lacduong/TacLINK/Experimental data/force_resconstruction/new/P0.0kPa_Trial5_1.PNG

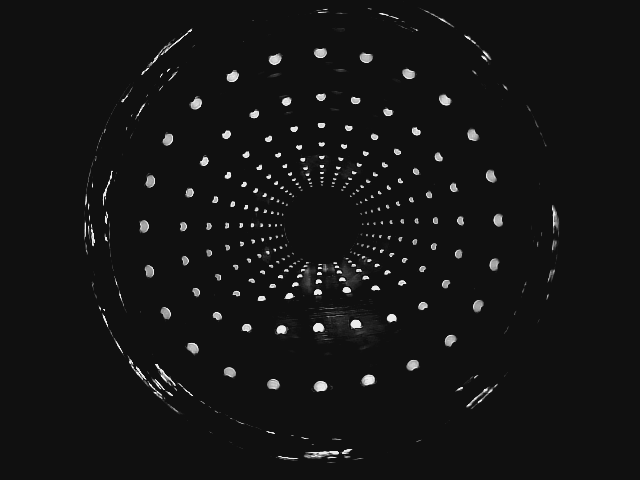
Experimental data/force_resconstruction/new/P0.0kPa_Trial5_1.PNG
