lacduong/TacLINK/Experimental data/force_resconstruction/new/P0.5kPa_Trial2_1.PNG

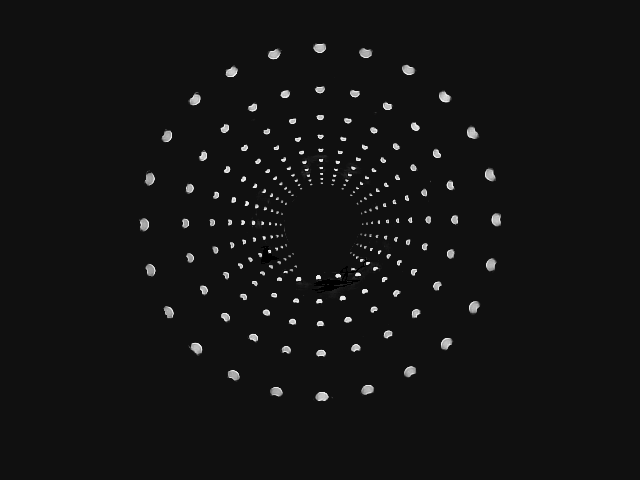
Experimental data/force_resconstruction/new/P0.5kPa_Trial2_1.PNG
