lacduong/TacLINK/Experimental data/final_experiment/ForceData/InitTrial001.CSV

Test No.
Title
Tester
Channel No. | 1 | 2 | 3 | 4
Channel Name | Fx-1 | Fy-1 | Fz-1 | Mark
Unit | N | N | N
Number of data | 150 | 150 | 150 | 150
maximum value | 0.02925 | 0.02603 | 0.03120 | 0
minimum value | -0.01497 | -0.01311 | -0.06188 | 0
0.000000 | 0.00000 | 0.00000 | 0.00000 | 0
0.100000 | 0.00000 | 0.00000 | 0.00000 | 0
0.200000 | 0.00000 | 0.00000 | 0.00000 | 0
0.300000 | 0.00000 | 0.00000 | 0.00000 | 0
0.400000 | 0.00000 | 0.00000 | 0.00000 | 0
0.500000 | 0.00000 | 0.00000 | 0.00000 | 0
0.600000 | -0.01447 | -0.00019 | -0.00008 | 0
0.700000 | -0.00031 | 0.00007 | -0.03104 | 0
0.800000 | -0.00025 | 0.01292 | 0.00013 | 0
0.900000 | 0.00000 | 0.00000 | 0.00000 | 0
1.000000 | 0.00000 | 0.00000 | 0.00000 | 0
1.100000 | 0.00000 | 0.00000 | 0.00000 | 0
1.200000 | 0.00000 | 0.00000 | 0.00000 | 0
1.300000 | 0.00000 | 0.00000 | 0.00000 | 0
1.400000 | 0.00000 | 0.00000 | 0.00000 | 0
1.500000 | -0.01447 | -0.00019 | -0.00008 | 0
1.600000 | 0.00000 | 0.00000 | 0.00000 | 0
1.700000 | -0.00025 | 0.01292 | 0.00013 | 0
1.800000 | -0.01447 | -0.00019 | -0.00008 | 0
1.900000 | -0.01422 | -0.01311 | -0.00021 | 0
2.000000 | -0.01447 | -0.00019 | -0.00008 | 0
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
