lacduong/TacLINK/Experimental data/final_experiment/ForceData/J10R5Trial002.CSV

Test No.
Title
Tester
Channel No. | 1 | 2 | 3 | 4
Channel Name | Fx-1 | Fy-1 | Fz-1 | Mark
Unit | N | N | N
Number of data | 444 | 444 | 444 | 444
maximum value | 0.01579 | 0.05157 | 0.15569 | 0
minimum value | -0.04266 | -0.00055 | 0.06235 | 0
0.000000 | 0.00132 | 0.01255 | 0.15535 | 0
0.100000 | 0.00132 | 0.01255 | 0.15535 | 0
0.200000 | 0.00106 | 0.02547 | 0.15548 | 0
0.300000 | 0.00132 | 0.01255 | 0.15535 | 0
0.400000 | 0.01553 | 0.02566 | 0.15556 | 0
0.500000 | 0.00075 | 0.02555 | 0.12444 | 0
0.600000 | 0.01579 | 0.01274 | 0.15543 | 0
0.700000 | 0.00075 | 0.02555 | 0.12444 | 0
0.800000 | 0.00100 | 0.01263 | 0.12431 | 0
0.900000 | 0.00075 | 0.02555 | 0.12444 | 0
1.000000 | -0.01372 | 0.02536 | 0.12437 | 0
1.100000 | 0.00075 | 0.02555 | 0.12444 | 0
1.200000 | -0.01372 | 0.02536 | 0.12437 | 0
1.300000 | 0.00075 | 0.02555 | 0.12444 | 0
1.400000 | 0.00075 | 0.02555 | 0.12444 | 0
1.500000 | 0.00075 | 0.02555 | 0.12444 | 0
1.600000 | 0.00106 | 0.02547 | 0.15548 | 0
1.700000 | 0.00075 | 0.02555 | 0.12444 | 0
1.800000 | 0.01522 | 0.02573 | 0.12452 | 0
1.900000 | -0.01397 | 0.03828 | 0.12450 | 0
2.000000 | 0.00075 | 0.02555 | 0.12444 | 0
2.100000 | 0.00100 | 0.01263 | 0.12431 | 0
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
