lacduong/TacLINK/Experimental data/final_experiment/Init/InitTrial5_1.PNG

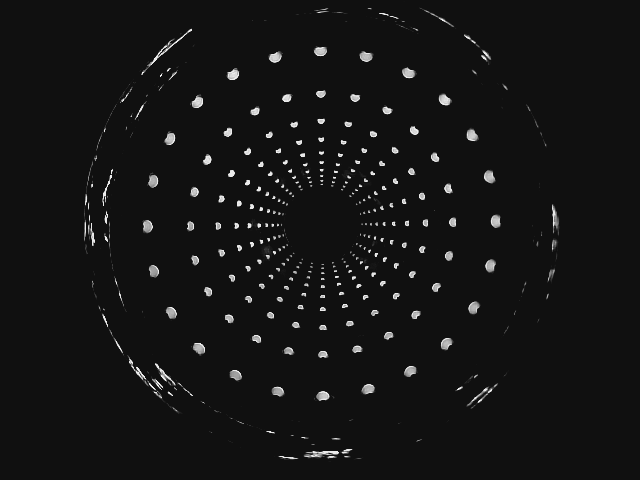
Experimental data/final_experiment/Init/InitTrial5_1.PNG
