lacduong/TacLINK/Experimental data/final_experiment/Init/InitTrial6_2.PNG

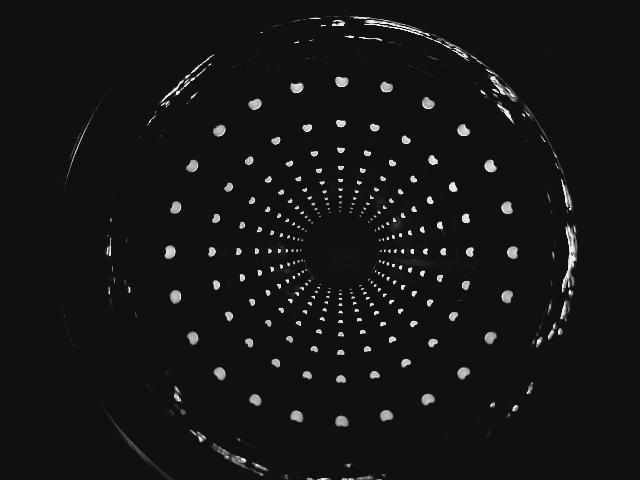
Experimental data/final_experiment/Init/InitTrial6_2.PNG
