lacduong/TacLINK/Experimental data/final_experiment/J5/J5R10Trial6_2.PNG

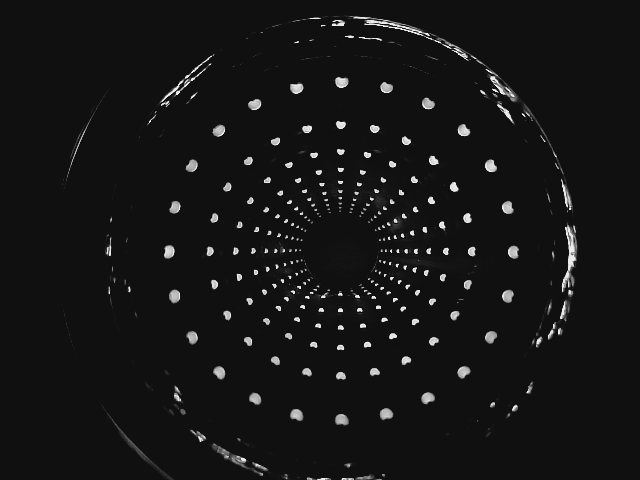
Experimental data/final_experiment/J5/J5R10Trial6_2.PNG
