lacduong/TacLINK/Experimental data/final_experiment/J9/J9R5Trial7cam2.PNG

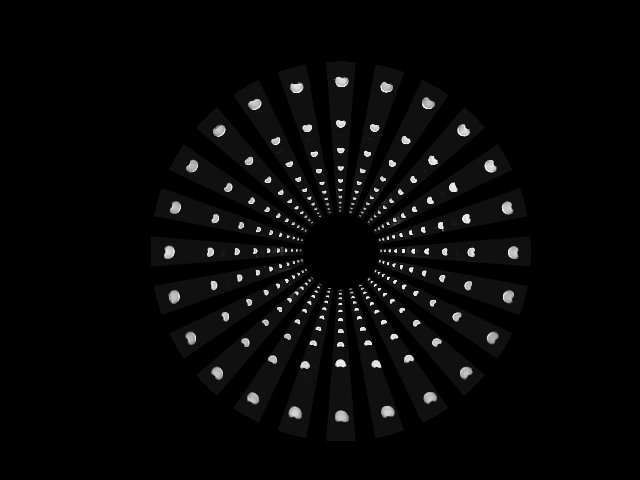
Experimental data/final_experiment/J9/J9R5Trial7cam2.PNG
