lacduong/TacLINK/Experimental data/source_force_data/J1/J1R0P0.0kPaTrial2cam1.PNG

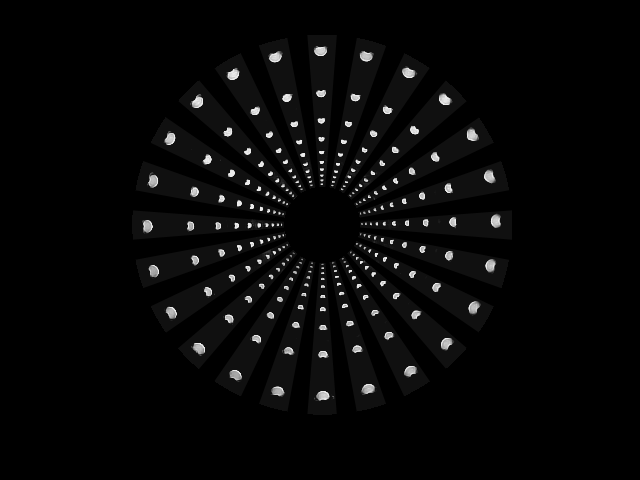
Experimental data/source_force_data/J1/J1R0P0.0kPaTrial2cam1.PNG
