lacduong/TacLINK/Experimental data/source_force_data/J1/J1R5P1.0kPaTrial8cam2.PNG

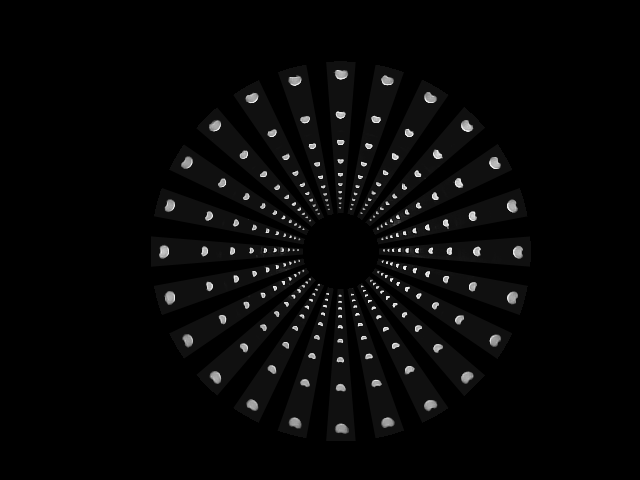
Experimental data/source_force_data/J1/J1R5P1.0kPaTrial8cam2.PNG
