lacduong/TacLINK/Experimental data/source_force_data/J1/R5/J1R5P0.5kPaTrial1cam1.PNG

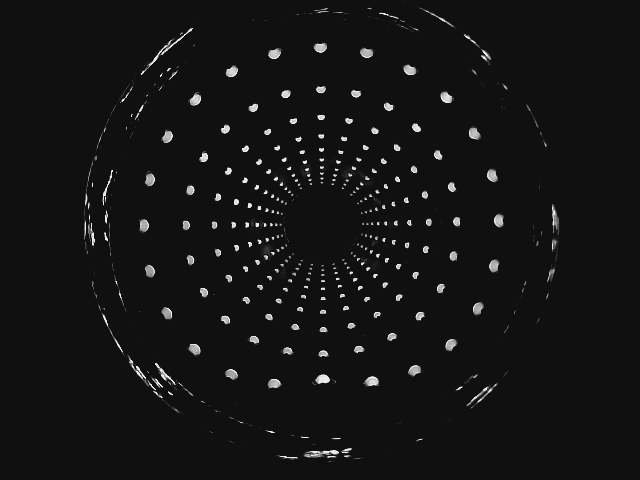
Experimental data/source_force_data/J1/R5/J1R5P0.5kPaTrial1cam1.PNG
