lacduong/TacLINK/Experimental data/source_force_data/J1/R5/J1R5P1.5kPaTrial4cam2.PNG

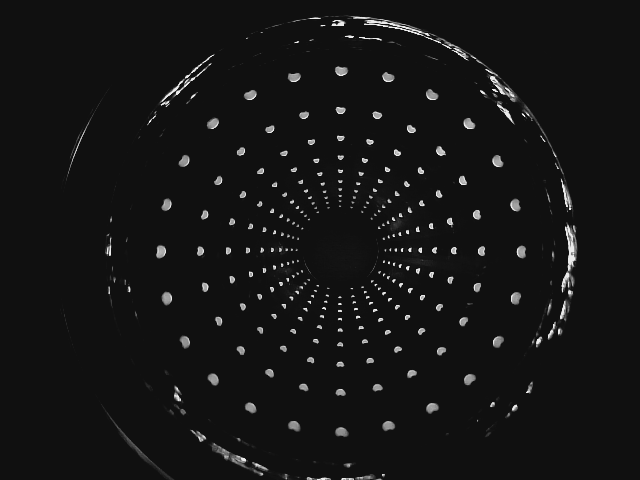
Experimental data/source_force_data/J1/R5/J1R5P1.5kPaTrial4cam2.PNG
