lacduong/TacLINK/Experimental data/source_force_data/J2/R5/J2R5P0.5kPaTrial3cam2.PNG

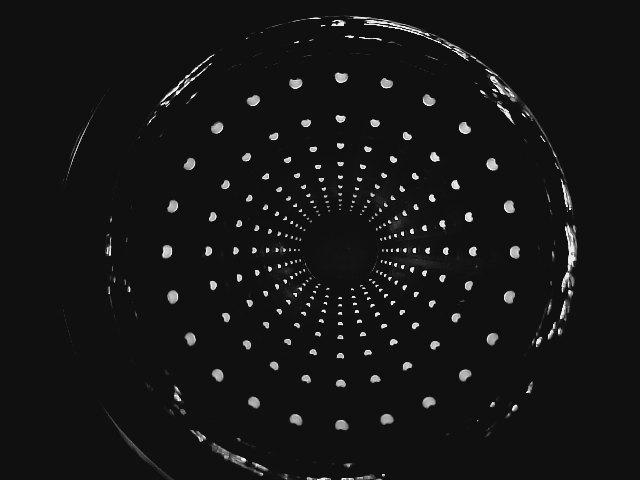
Experimental data/source_force_data/J2/R5/J2R5P0.5kPaTrial3cam2.PNG
