lacduong/TacLINK/Experimental data/source_force_data/J2/R10/J2R10P1.0kPaTrial4cam2.PNG

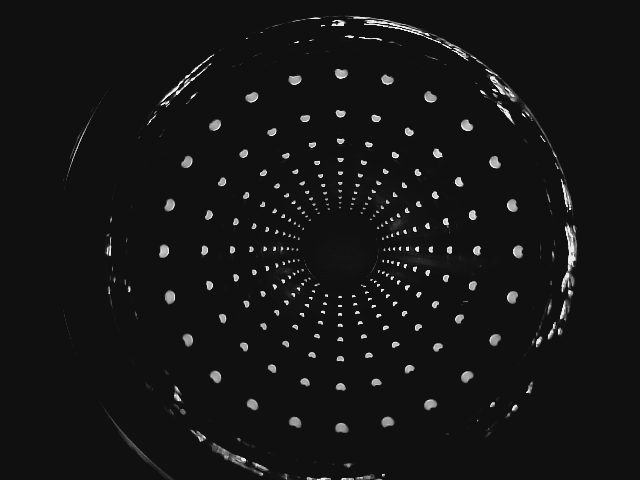
Experimental data/source_force_data/J2/R10/J2R10P1.0kPaTrial4cam2.PNG
