lacduong/TacLINK/Experimental data/source_force_data/J4/R10/J4R10P1.5kPaTrial7cam1.PNG

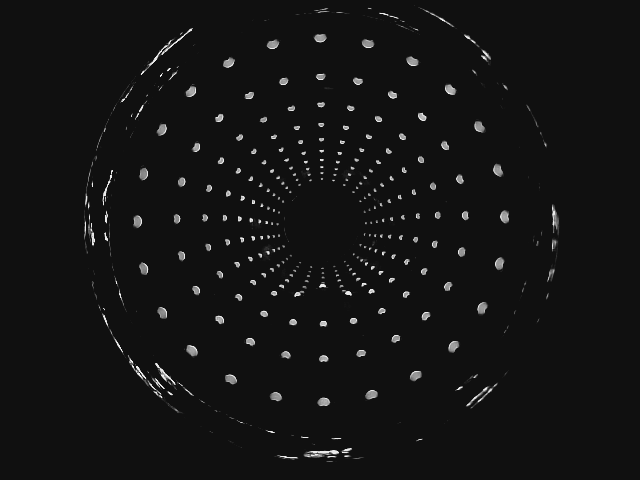
Experimental data/source_force_data/J4/R10/J4R10P1.5kPaTrial7cam1.PNG
