lacduong/TacLINK/Experimental data/source_force_data/J6/R5/J6R5P1.5kPaTrial8cam1.PNG

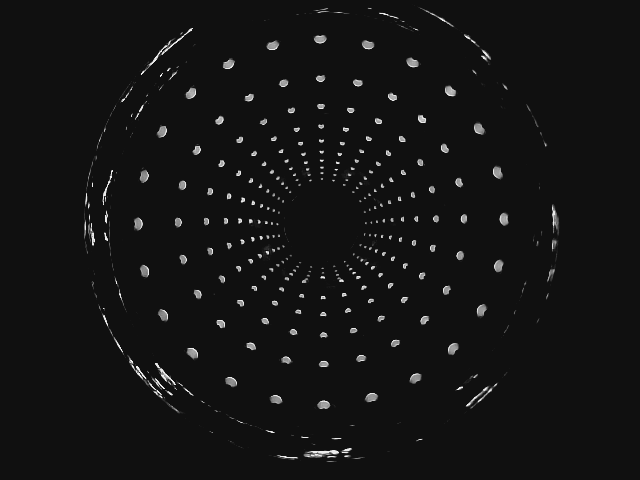
Experimental data/source_force_data/J6/R5/J6R5P1.5kPaTrial8cam1.PNG
