lacduong/TacLINK/Experimental data/source_force_data/J8/R5/J8R5P1.0kPaTrial9cam2.PNG

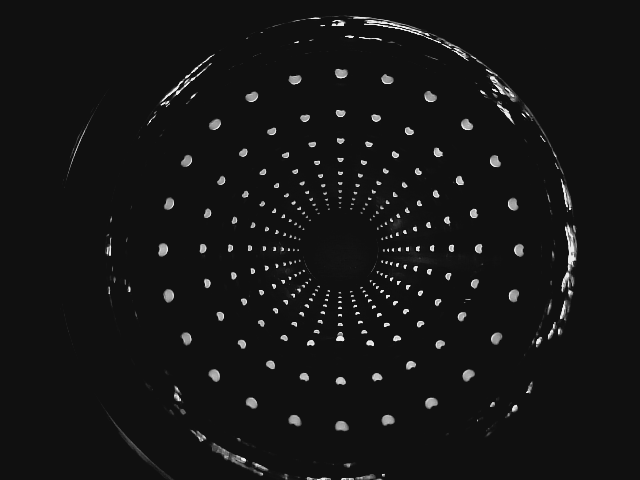
Experimental data/source_force_data/J8/R5/J8R5P1.0kPaTrial9cam2.PNG
