lacduong/TacLINK/Experimental data/source_force_data/J8/R10/J8R10P0.5kPaTrial1cam2.PNG

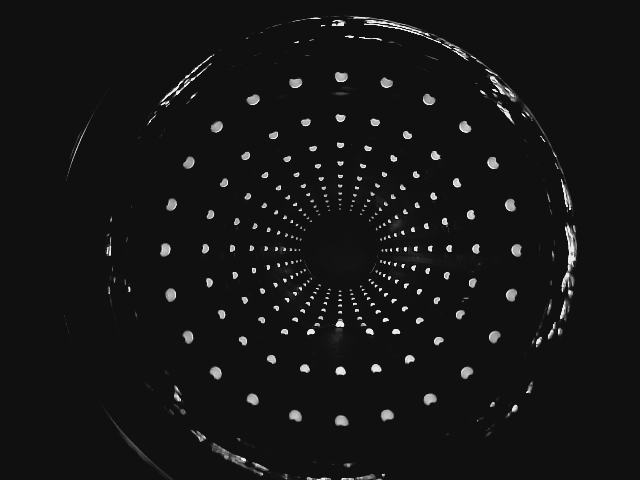
Experimental data/source_force_data/J8/R10/J8R10P0.5kPaTrial1cam2.PNG
