lacduong/TacLINK/Experimental data/source_force_data/J10/J10R5P0.0kPaTrial7cam2.PNG

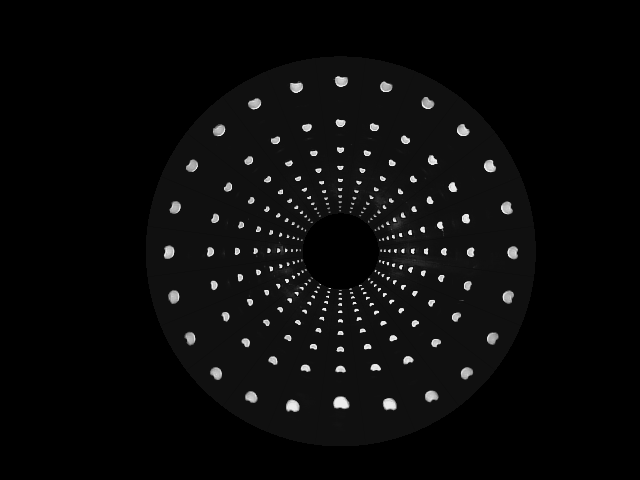
Experimental data/source_force_data/J10/J10R5P0.0kPaTrial7cam2.PNG
