lacduong/TacLINK/Experimental data/source_force_data/J10/J10R5P1.0kPaTrial2cam1.PNG

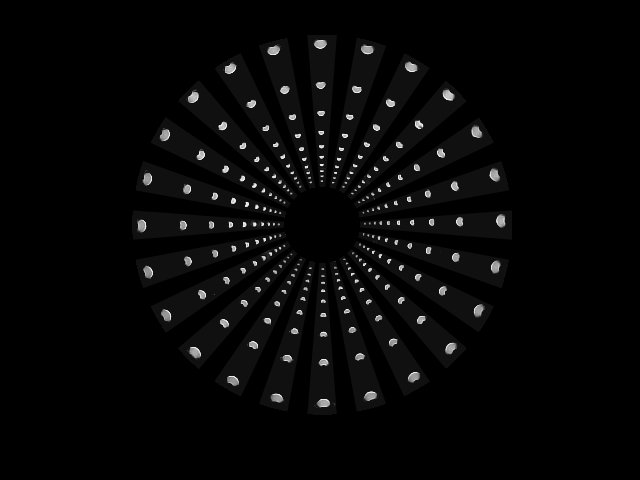
Experimental data/source_force_data/J10/J10R5P1.0kPaTrial2cam1.PNG
