lacduong/TacLINK/IEEE T-RO Final Latex Version/camera_tracking.pdf

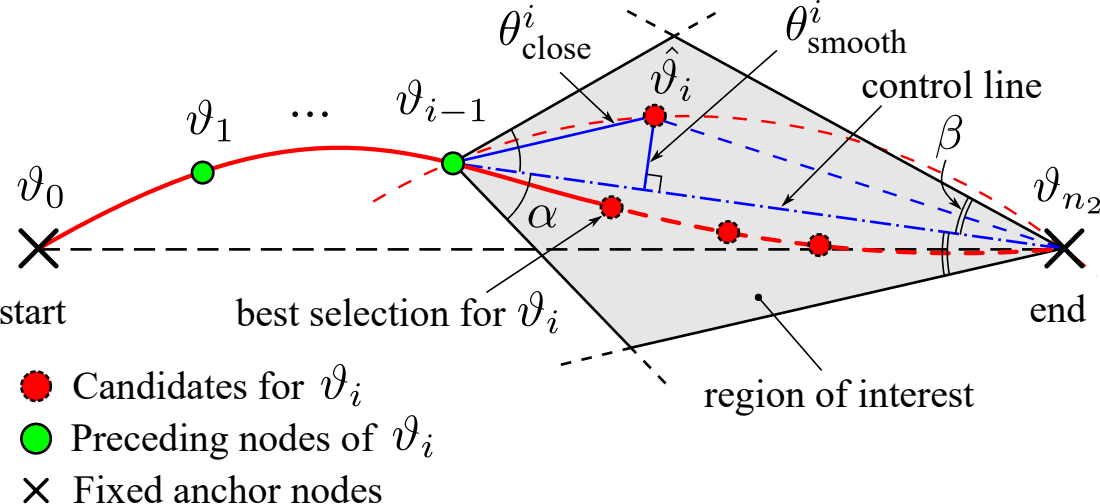
[picture p59: page 1]
smooth; start; end; close; control line

Candidates for
Preceding nodes of
Fixed anchor nodes

best selection for

region of interest
