lacduong/TacLINK/IEEE T-RO Final Latex Version/camera_variation.pdf

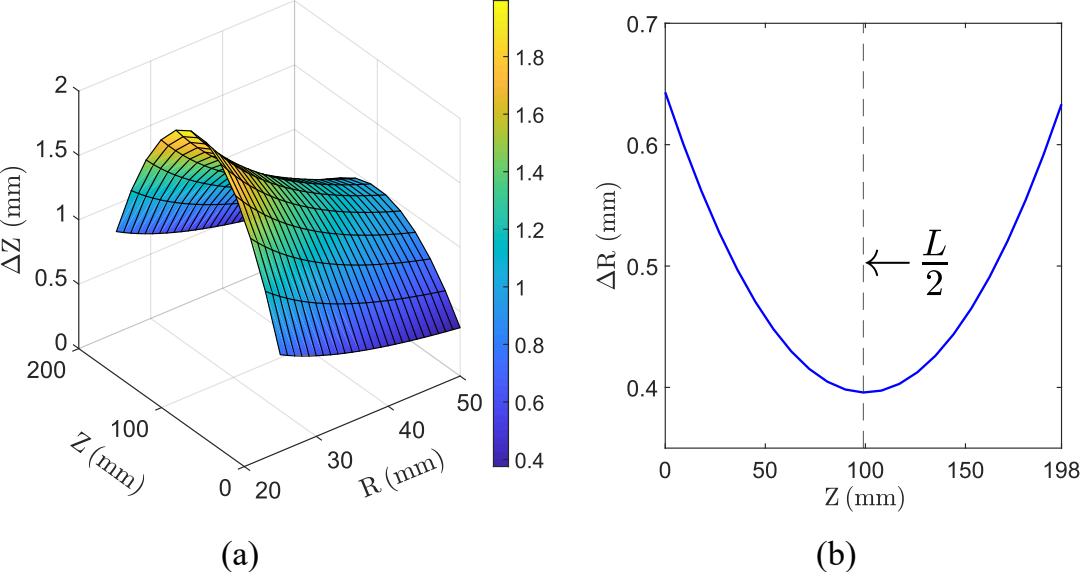
[picture p60: page 1]
