lacduong/TacLINK/IEEE T-RO Final Latex Version/fem_model.pdf

e

# cell

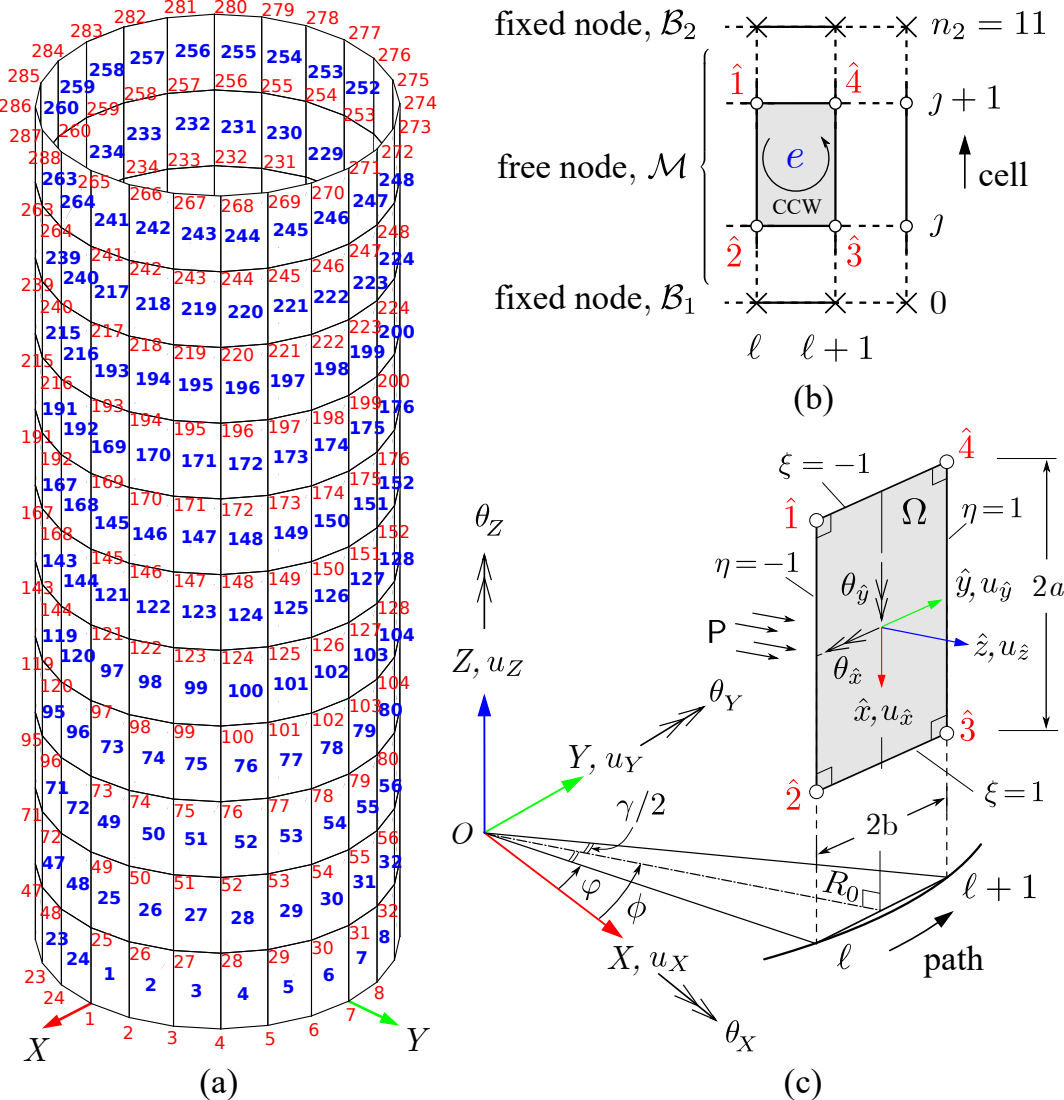
[picture p61: page 1]
CCW; path; fixed node; free node
