lacduong/TacLINK/IEEE T-RO Final Latex Version/fem_simulation.pdf

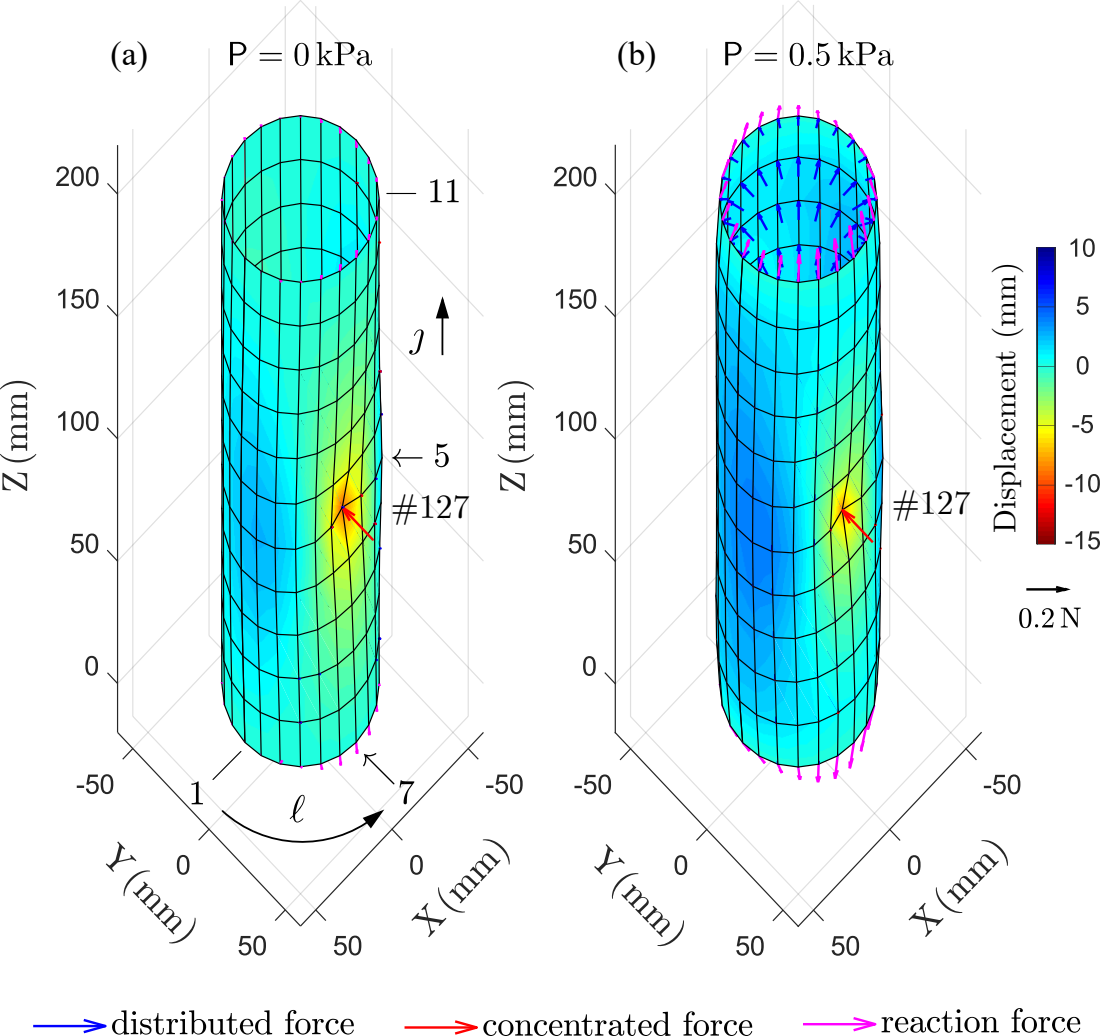
[picture p62: page 1]
Displacement (mm)
