lacduong/TacLINK/IEEE T-RO Final Latex Version/force_singlepoint.pdf

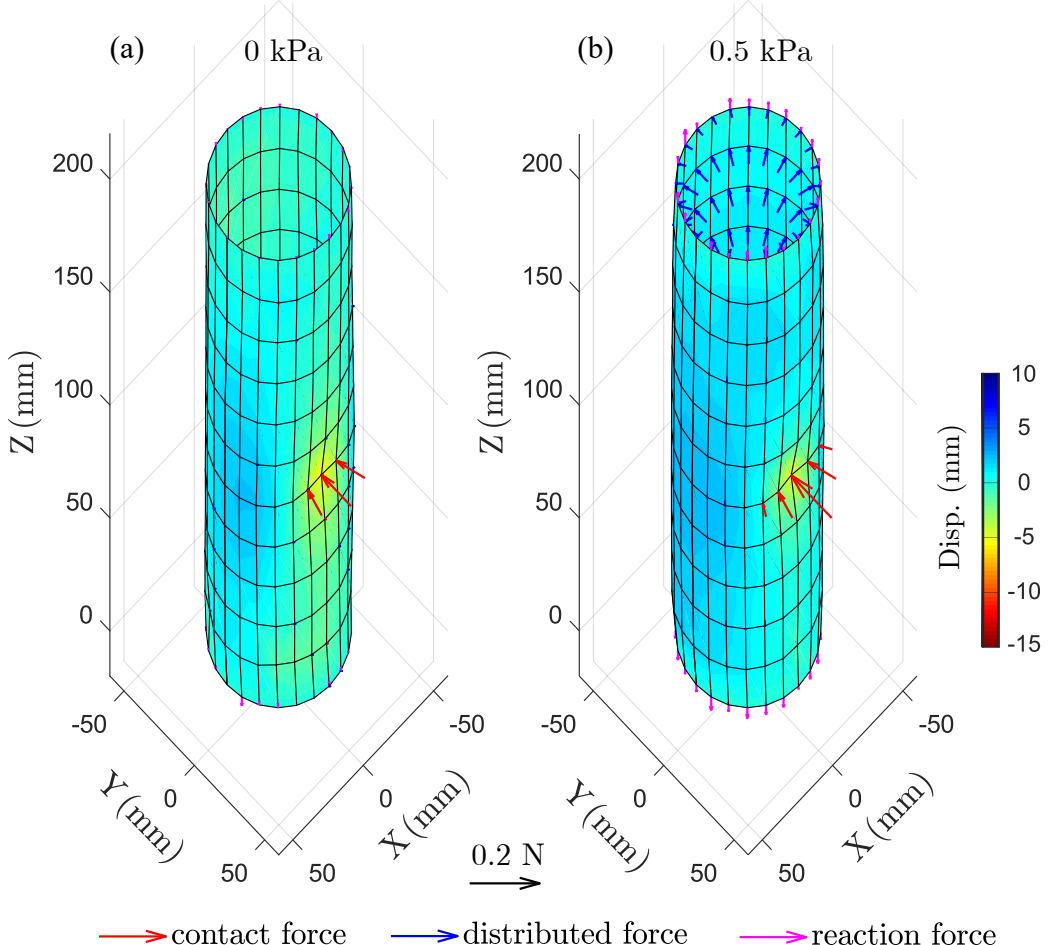
[picture p63: page 1]
Disp. (mm); kPa; 0.5 kPa
